sparkfun/MicroMod_Asset_Tracker/Examples/AssetTracker_Example29_TCPSocketPingPong/AssetTrackerPins.h

/*

  MicroMod Asset Tracker Pin & Port Definitions
  =============================================

  Written by: Paul Clark
  Date: December 28th 2021

  The file defines the pins and ports for the MicroMod Asset Tracker.

  The pin and ports are defined using the MicroMod naming scheme.
  This allows the code to run on different MicroMod Processor Boards
  without needing to change the pin numbers.

  Licence: MIT
  Please see the LICENSE.md for full details

*/

/*

 Notes:

  Artemis PB enables RTS/CTS hardware handshaking by default. So we do not need to define those pins here.
  Artemis PB does not support TX2 (SARA_DTR) or RX2 (SARA_DCD) and so cannot use the SARA's 2-UART mode.

  SAMD51 PB does not support RTS (SARA_RTS) or CTS (SARA_CTS). So we do not need to define those pins here.
  SAMD51 PB does support TX2 (SARA_DTR) and RX2 (SARA_DCD) and so can probably use the SARA's 2-UART mode.
    But the pins are shared with I2C_SCL1 so care needs to be taken when closing the SARA_SCL and SARA_SDA
    split pads (so the PB can monitor the SARA's I2C bus).

  ESP32 PB does not support RTS (SARA_RTS) or CTS (SARA_CTS). So we do not need to define those pins here.
  ESP32 PB does not support TX2 (SARA_DTR) or RX2 (SARA_DCD) and so cannot use the SARA's 2-UART mode.
  ESP32 PB connects G1->AUD_LRCLK->SCL1 and G2->AUD_BCLK->SDA1 and so a decision is required:
    If the user needs access to the digital microphone, the MICROSD_PWR_EN and SARA_PWR pins need to be isolated.
    The user can open the PDM_CLK and PDM_DAT split pads to isolate the microphone if required.
    Or can open the G1/SD_PWR and G2/LTE_PWR split pads to isolate the power enables. Both enables will then default to ON.
  ESP32 PB connects G3->TX1->AUD_OUT and G4->RX1->AUD_IN and so the ICM_PWR_EN and SARA_RI pins must be isolated:
    The G3/IMU_PWR and G4/RI split pads are normally open. The IMU power will default to ON.
  ESP32 PB: G7, G9 and G10 are not connected. So SARA_DSR and SARA_ON are not supported.

  STM32 PB does not support RTS/CTS hardware handshaking. So we do not need to define those pins here.
  STM32 PB does not support TX2 (SARA_DTR) or RX2 (SARA_DCD) and so cannot use the SARA's 2-UART mode.
  STM32 PB: G7 is not connected. So SARA_ON is not supported.

*/

// Ports

#define SD_and_IMU_SPI SPI  // SPI interface used by the Micro SD card and IMU
#define SARA_Serial Serial1 // Serial interface used by the SARA
#define AT_Wire Wire        // Wire (I2C) interface used by the Qwiic bus and the Battery Fuel Gauge

// Only some of the PBs support a second UART
#if defined(ARDUINO_AM_AP3_SFE_ARTEMIS_MICROMOD) || defined(ARDUINO_ARCH_SAMD) || defined(ARDUINO_ARCH_ESP32) || defined(ARDUINO_ARCH_STM32)
#define SARA_2UART_MODE_NOT_SUPPORTED
#endif

// Fix for v2 of Apollo3 (Artemis)
#if defined(ARDUINO_APOLLO3_SFE_ARTEMIS_MM_PB)
#define I2CINT I2C_INT
#define CS SS
#define BATTVIN3 BATT_VIN
#endif

// This is hopefully a temporary fix for the SAMD51 pins
#if defined(ARDUINO_ARCH_SAMD)
#define BATTVIN3 BATT_VIN
#endif

// This is hopefully a temporary fix for the ESP32 pins
#if defined(ARDUINO_ARCH_ESP32)
#define G7 -1
#define I2CINT I2C_INT
#define CS SS
#define BATTVIN3 BATT_VIN
#endif

// This is hopefully a temporary fix for the nRF52840 pins
#if defined(ARDUINO_ARDUINO_NANO33BLE)
#define I2CINT PIN_WIRE_INT
#define CS SS
#endif

#if defined(ARDUINO_ARCH_STM32)
#define G7 -1
#define I2CINT INT
#define CS PIN_SPI_SS
#define BATTVIN3 2 // == A2 == PA_1
HardwareSerial Serial1(RX1, TX1);
#endif

// Pins

// Pre-defined MicroMod PB I/O pins:
// D0   : I/O : intented to be used as the Chip Select for an external SPI device
// D1   : I/O
// A0   : I/O : can be used for analog input
// A1   : I/O : can be used for analog input
// PWM0 : I/O : can be used for PWM output
// PWM1 : I/O : can be used for PWM output

const int EXT_SPI_CS = D0; // Output: Active low

const int MICROSD_CS     = G0; // Output: Active low
const int MICROSD_PWR_EN = G1; // Output: Pull low to enable power for the SD card. Pull high to disable.
const int SARA_PWR       = G2; // Output: Pull high then low to switch the SARA-R5 on. Pull high for five seconds then low again to switch it off.
const int IMU_PWR_EN     = G3; // Output: Pull high to enable power for the IMU. Pull low to disable.
const int SARA_RI        = G4; // Input:  SARA-R5 Ring Indicator pin. Becomes CTS2 in 2-UART mode.
const int SARA_INT       = G5; // Input:  SARA-R5 EXT_INT interrupt pin.
const int SARA_ON        = G6; // Input:  Pulled low when the SARA-R5 is on. Pulled high when the SARA-R5 is off.
const int SARA_DSR       = G7; // Input:  SARA-R5 DSR pin. Becomes RTS2 (Output) in 2-UART mode. (Change the split pad to change the direction of the 74AVC4T774)

#if defined(ARDUINO_ARDUINO_NANO33BLE)
const int SARA_RTS = PIN_SERIAL_RTS1; // Output: SARA-R5 RTS pin.
const int SARA_CTS = PIN_SERIAL_CTS1; // Input:  SARA-R5 CTS pin.
const int SARA_DTR = PIN_SERIAL_TX2; // Output: SARA-R5 DTR pin. Becomes TXD2 in 2-UART mode.
const int SARA_DCD = PIN_SERIAL_RX2; // Input:  SARA-R5 DCD pin. Becomes RXD2 in 2-UART mode.
#endif

const int IMU_INT = I2CINT; // Input: IMU interrupt pin
const int IMU_CS = CS; // Output: IMU SPI Chip Select

const int VIN_DIV_3 = BATTVIN3; // Analog input: VIN supply voltage divided by 3.
